WiseLord/matrixclock/src/font-cp1251-08.c

#include "fonts.h"

#include <avr/pgmspace.h>

const uint8_t font_cp1251_08[] PROGMEM = {
    0x00, 0x00, 0x00, 0x00, VOID,       // 0x20 =>
    0x5F, VOID, VOID, VOID, VOID,       // 0x21 => !
    0x07, 0x00, 0x07, VOID, VOID,       // 0x22 => "
    0x14, 0x7F, 0x14, 0x7F, 0x14,       // 0x23 => #
    0x24, 0x2A, 0x7F, 0x2A, 0x12,       // 0x24 => $
    0x23, 0x13, 0x08, 0x64, 0x62,       // 0x25 => %
    0x36, 0x49, 0x55, 0x22, 0x50,       // 0x26 => &
    0x05, 0x03, VOID, VOID, VOID,       // 0x27 => '
    0x1C, 0x22, 0x41, VOID, VOID,       // 0x28 => (
    0x41, 0x22, 0x1C, VOID, VOID,       // 0x29 => )
    0x14, 0x08, 0x3E, 0x08, 0x14,       // 0x2A => *
    0x08, 0x08, 0x3E, 0x08, 0x08,       // 0x2B => +
    0x80, 0x40, VOID, VOID, VOID,       // 0x2C => ,
    0x08, 0x08, 0x08, 0x08, VOID,       // 0x2D => -
    0x40, VOID, VOID, VOID, VOID,       // 0x2E => .
    0x20, 0x10, 0x08, 0x04, 0x02,       // 0x2F => /

    0x3E, 0x41, 0x41, 0x3E, VOID,       // 0x30 => 0
    0x00, 0x42, 0x7F, 0x40, VOID,       // 0x31 => 1
    0x42, 0x61, 0x51, 0x4E, VOID,       // 0x32 => 2
    0x22, 0x41, 0x49, 0x36, VOID,       // 0x33 => 3
    0x18, 0x14, 0x12, 0x7F, VOID,       // 0x34 => 4
    0x27, 0x45, 0x45, 0x39, VOID,       // 0x35 => 5
    0x3E, 0x49, 0x49, 0x32, VOID,       // 0x36 => 6
    0x01, 0x71, 0x09, 0x07, VOID,       // 0x37 => 7
    0x36, 0x49, 0x49, 0x36, VOID,       // 0x38 => 8
    0x26, 0x49, 0x49, 0x3E, VOID,       // 0x39 => 9
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
    0x7C, 0x50, 0x20, 0x00, 0x7C,       // 0xFB => ы
    0x7C, 0x50, 0x50, 0x20, VOID,       // 0xFC => ь
    0x28, 0x44, 0x54, 0x54, 0x38,       // 0xFD => э
    0x7C, 0x10, 0x38, 0x44, 0x38,       // 0xFE => ю
    0x08, 0x54, 0x34, 0x14, 0x7C,       // 0xFF => я
};
