WiseLord/matrixclock/editor/defines.h

#ifndef DEFINES_H
#define DEFINES_H

#define ORGANIZATION_NAME           "WiseLord"
#define ORGANIZATION_DOMAIN         "github.io"
#define APPLICATION_NAME            "Matrixclock"

#define SETTINGS_GENERAL            "General"
#define SETTINGS_GENERAL_LANGUAGE   "General/Language"

#endif // DEFINES_H
