WiseLord/matrixclock/src/font-smallnum.c

#include "fonts.h"

#include <avr/pgmspace.h>

const uint8_t font_smallnum[] PROGMEM = {
    0x7C, 0x44, 0x7C,       // 0xF0 => 0
    0x48, 0x7C, 0x40,       // 0xF1 => 1
    0x74, 0x54, 0x5C,       // 0xF2 => 2
    0x54, 0x54, 0x7C,       // 0xF3 => 3
    0x1C, 0x10, 0x7C,       // 0xF4 => 4
    0x5C, 0x54, 0x74,       // 0xF5 => 5
    0x7C, 0x54, 0x74,       // 0xF6 => 6
    0x04, 0x04, 0x7C,       // 0xF7 => 7
    0x7C, 0x54, 0x7C,       // 0xF8 => 8
    0x5C, 0x54, 0x7C,       // 0xF9 => 9
};
