WiseLord/matrixclock/src/rtc.h

#ifndef RTC_H
#define RTC_H

#include <inttypes.h>

#define RTC_I2C_ADDR        0xD0

enum {
    RTC_SEC = 0,
    RTC_MIN,
    RTC_HOUR,
    RTC_WDAY,
    RTC_DATE,
    RTC_MONTH,
    RTC_YEAR,
    RTC_ETM,
};

typedef struct {
    int8_t sec;
    int8_t min;
    int8_t hour;
    int8_t wday;
    int8_t date;
    int8_t month;
    int8_t year;
    int8_t etm;
} RTC_type;

extern RTC_type rtc;

#define RTC_NOEDIT          0xFF

void rtcReadTime(void);
void rtcCorrSec(void);
void rtcNextEditParam(void);
void rtcChangeTime(int8_t diff);

uint8_t rtcBinDecToDec(uint8_t num);
uint8_t rtcDecToBinDec(uint8_t num);

#endif // RTC_H
